gitaroktato/local-llm/img/gpu-mount-screw.jpg

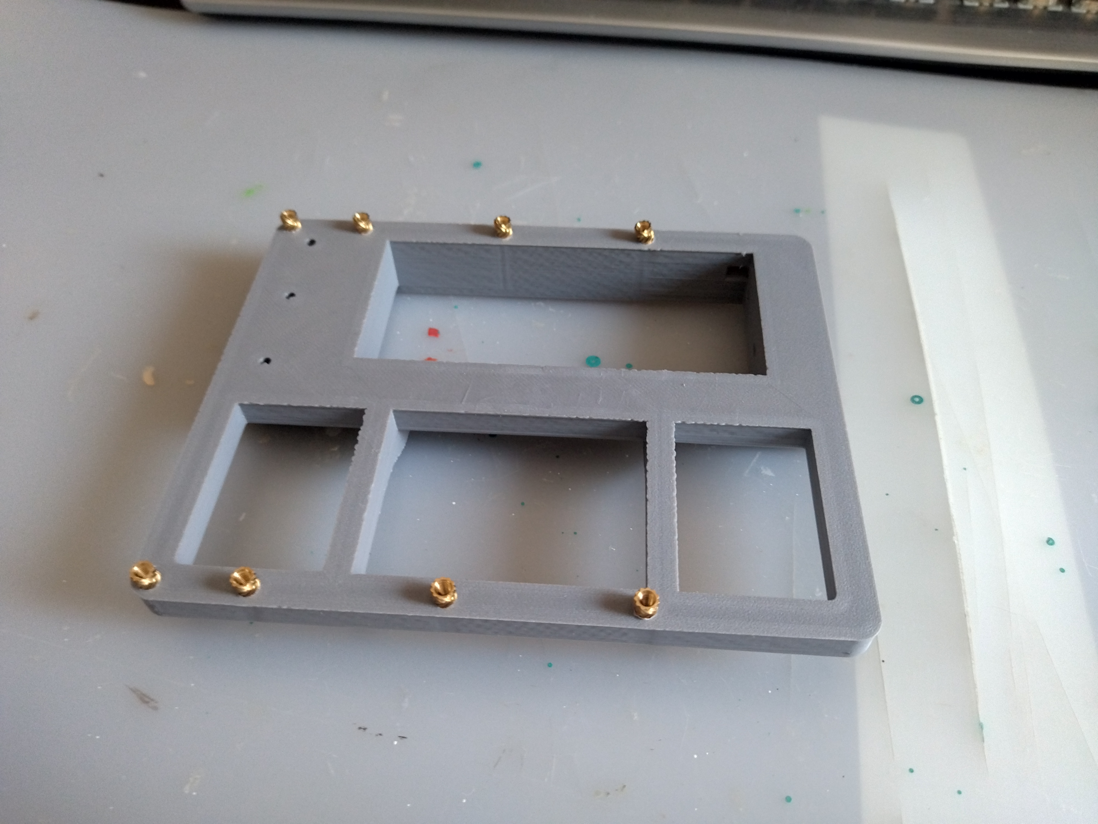
img/gpu-mount-screw.jpg
