gitaroktato/local-llm/img/gpu-mount-short-1.jpg

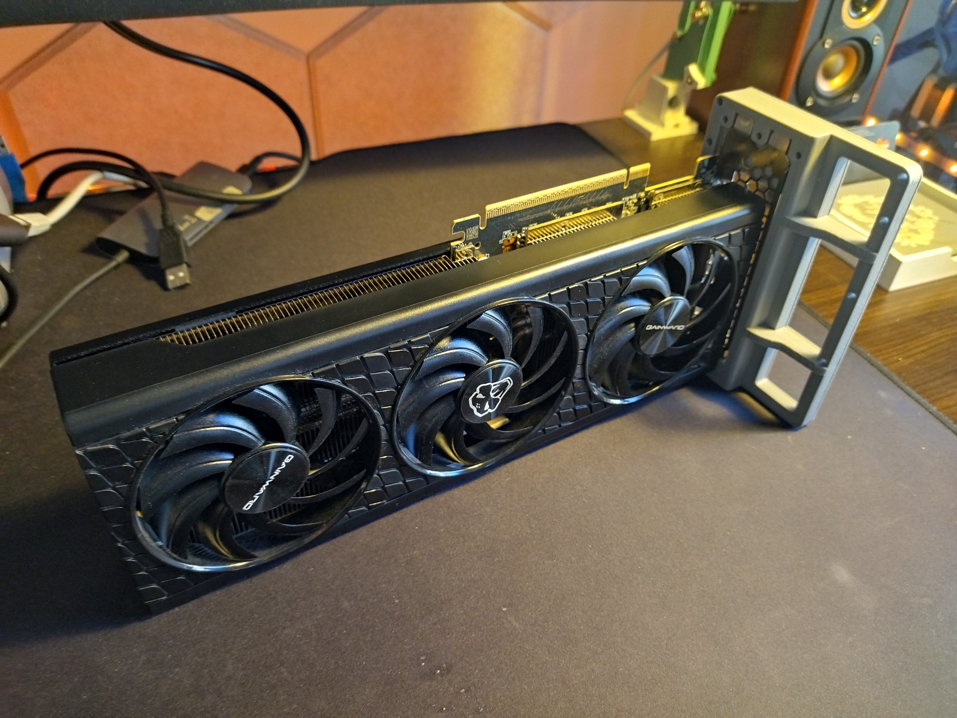
img/gpu-mount-short-1.jpg
