gitaroktato/local-llm/img/gpu-mount-vertical.jpg

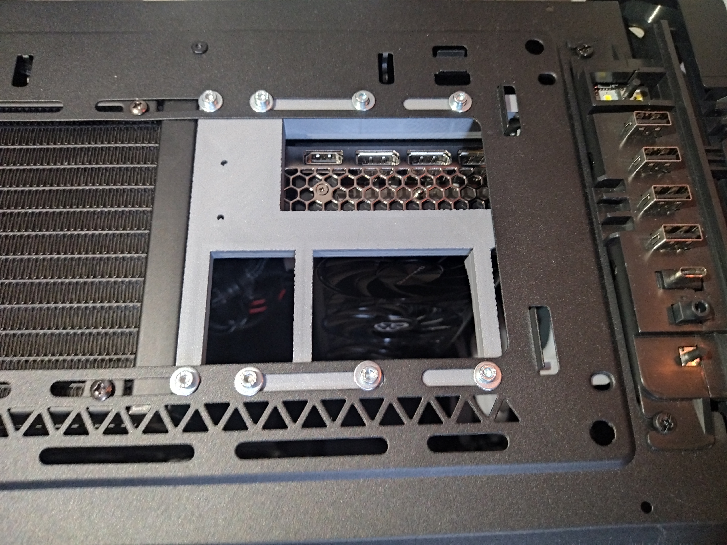
img/gpu-mount-vertical.jpg
