gitaroktato/local-llm/img/gpu-mount.jpg

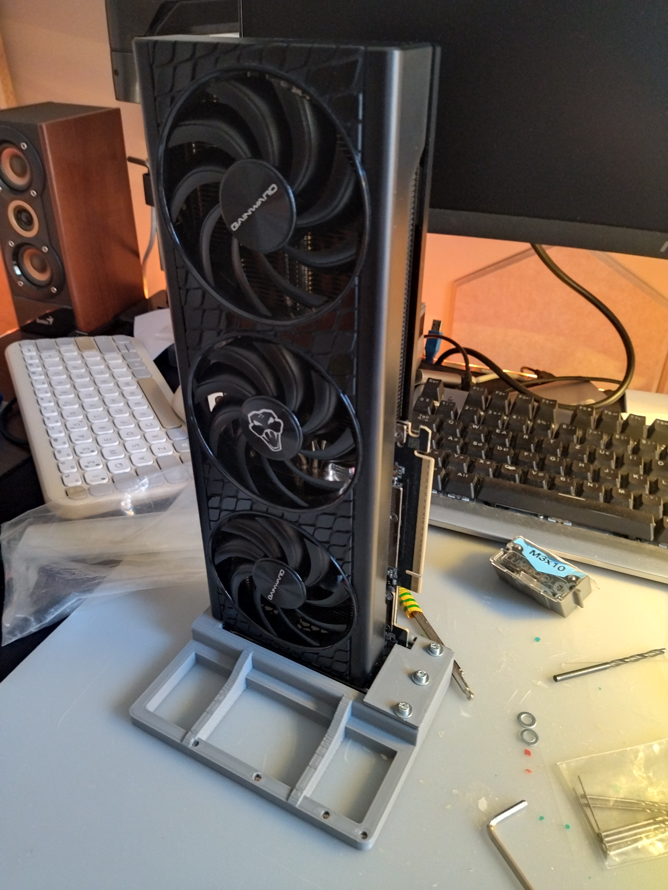
img/gpu-mount.jpg
