gitaroktato/local-llm/img/pcie5-flex.jpg

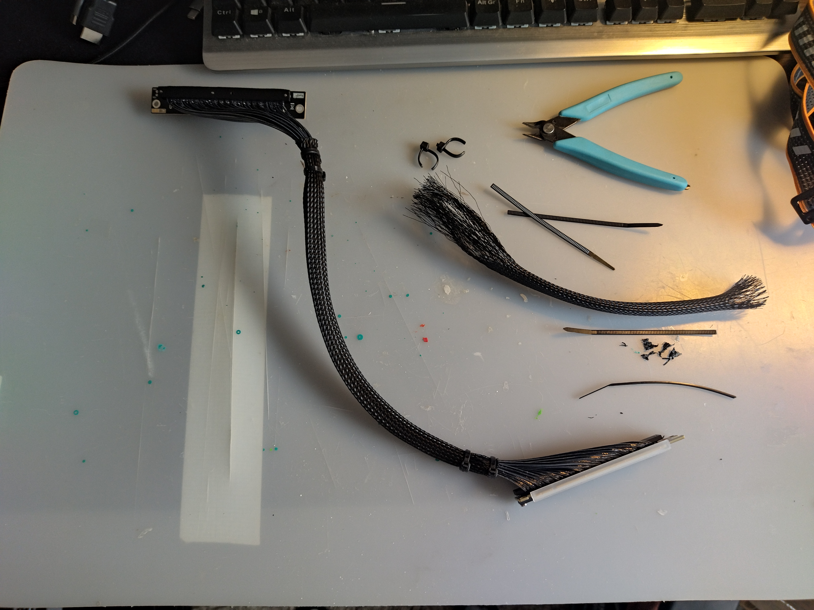
img/pcie5-flex.jpg
