gitaroktato/local-llm/img/pcie-flex2.jpg

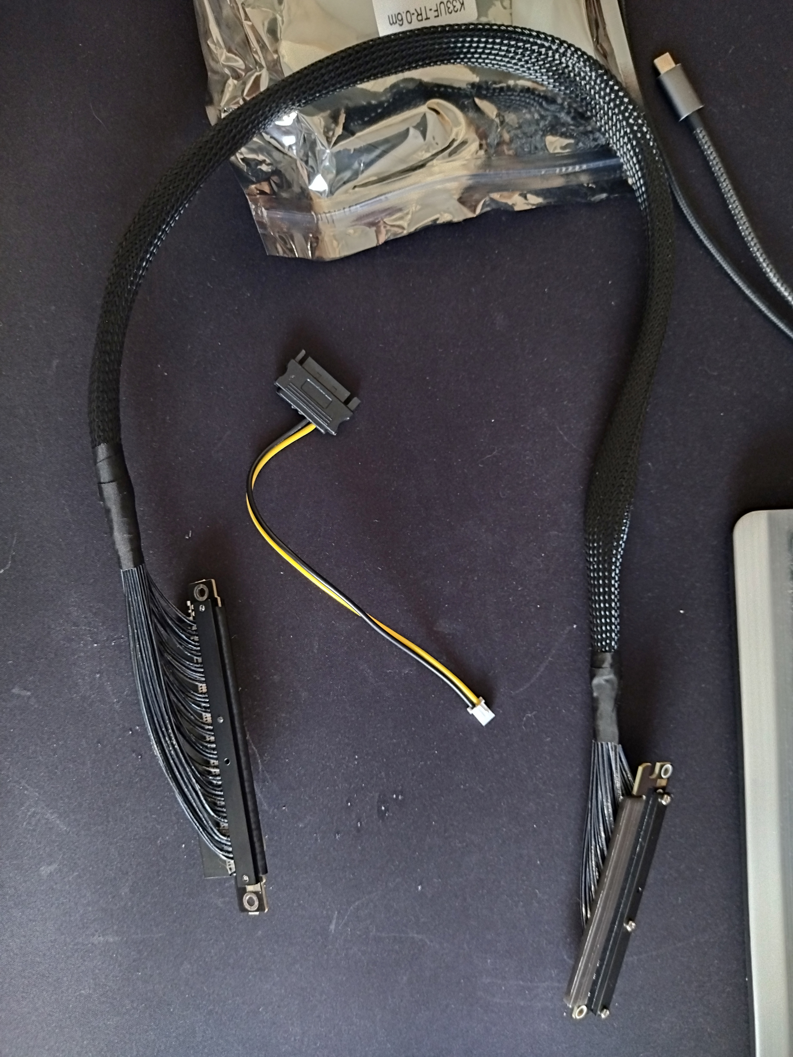
img/pcie-flex2.jpg
